fruchti/leshy/demo/hd44780/src/pinning.h

#pragma once

// Port A
#define PIN_LCD_RS              2   // PA2  - HD44780 register select
#define PIN_LCD_EN              3   // PA3  - HD44780 enable line
#define PIN_LCD_D4              4   // PA4  - HD44780 D4
#define PIN_LCD_D5              5   // PA5  - HD44780 D5
#define PIN_LCD_D6              6   // PA6  - HD44780 D6
#define PIN_LCD_D7              7   // PA7  - HD44780 D7
