fruchti/leshy/demo/ws2812b-hsv/src/pinning.h

#pragma once

#define PIN_POT_H               0   // PA0:  ADC_IN0
#define PIN_POT_S               1   // PA1:  ADC_IN1
#define PIN_POT_V               2   // PA2:  ADC_IN2
#define PIN_LED_DO              10  // PA10: TIM1_CH3
