fruchti/leshy/demo/soldering_station/src/config.h

#pragma once

#define CONFIG_MAX_TEMP             450     // °C
#define CONFIG_MIN_TEMP             50      // °C
#define CONFIG_DEFAULT_TEMP         350     // °C

#define CONFIG_BLINK_PERIOD         75      // ms
#define CONFIG_SET_DISPLAY_TIME     1000    // ms
#define CONFIG_BUILD_DISPLAY_TIME   20      // ms
#define CONFIG_SEGMENT_TEST_TIME    20      // ms
#define CONFIG_UPDATE_INTERVAL      200     // ms
