fruchti/leshy/demo/soldering_station/src/main.h

#pragma once

#include <stdbool.h>
#include "stm32f030x6.h"
#include "pinning.h"
#include "buildid.h"
#include "display.h"
#include "encoder.h"
#include "pid.h"
#include "config.h"
#include "nvs.h"

int main(void);
